ahmsville/Ahmsville-Dial-V2/AhmsvilleDial_v2/examples/Absolute_Variant_main/load_configurations.ino

void Load_Configurations() {
void (*config_arr[])() = {
AltiumSpecial,
Altium,
Blender,
Default,
Fusion_360,
Google_Docs,
PCB_Editor,
Premiere_Pro,
SOLIDWORKS,
Horizon
};
for (int i = 0; i < maxconfignum; i++) {
(*config_arr[i])();
 }
 }
